anamar19/Open-Book/Images/Display.png

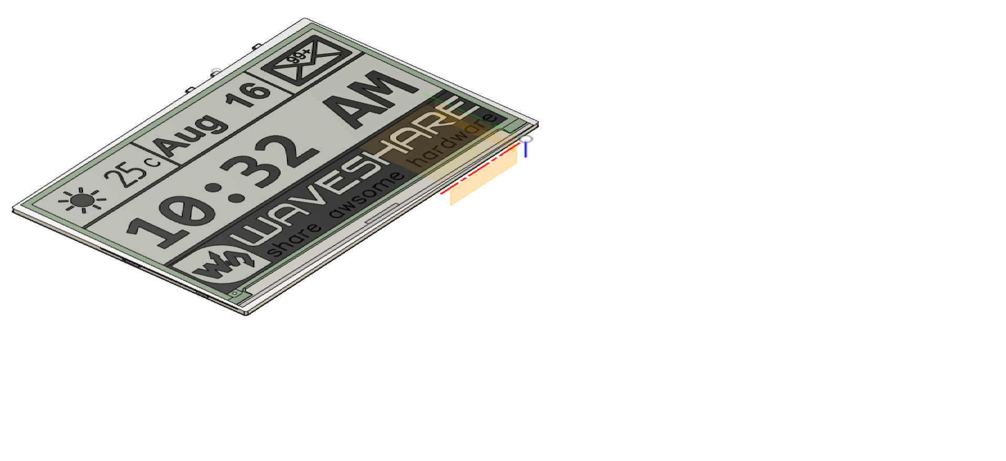
Images/Display.png
